rc-kid/rckid-v1/assets/backgrounds/unicorns-black.png

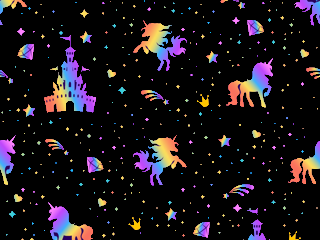
assets/backgrounds/unicorns-black.png
