rc-kid/rckid-v1/assets/heart-white.png

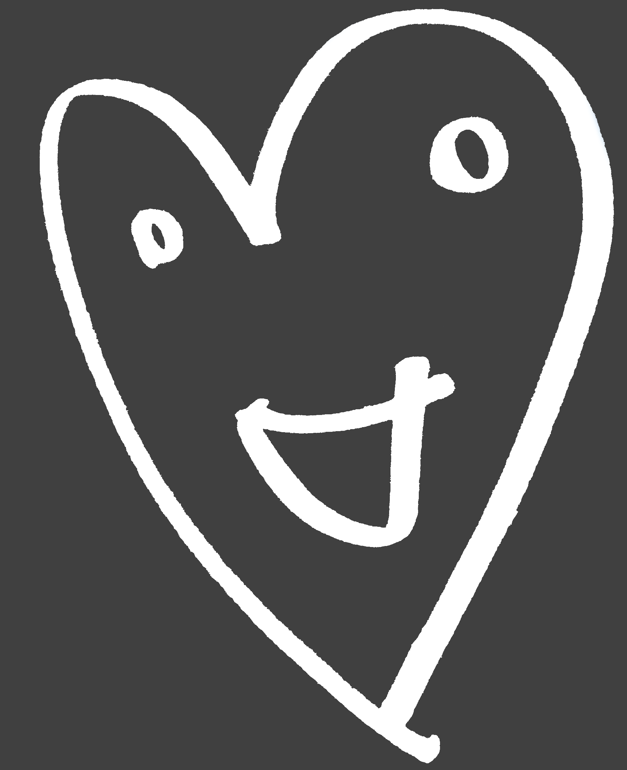
assets/heart-white.png
