rc-kid/rckid-v1/assets/images/001-game-controller.png

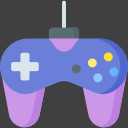
assets/images/001-game-controller.png
