rc-kid/rckid-v1/assets/images/002-rc-car.png

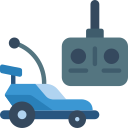
assets/images/002-rc-car.png
