rc-kid/rckid-v1/assets/images/004-flashlight.png

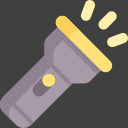
assets/images/004-flashlight.png
