rc-kid/rckid-v1/assets/images/006-baby-crib.png

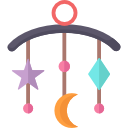
assets/images/006-baby-crib.png
