rc-kid/rckid-v1/assets/images/008-unicorn.png

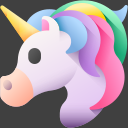
assets/images/008-unicorn.png
