rc-kid/rckid-v1/assets/images/010-high-volume.png

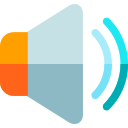
assets/images/010-high-volume.png
