rc-kid/rckid-v1/assets/images/011-power-off.png

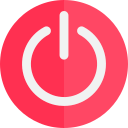
assets/images/011-power-off.png
