rc-kid/rckid-v1/assets/images/012-airplane-mode.png

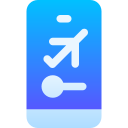
assets/images/012-airplane-mode.png
