rc-kid/rckid-v1/assets/images/014-info.png

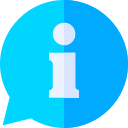
assets/images/014-info.png
