rc-kid/rckid-v1/assets/images/020-poo.png

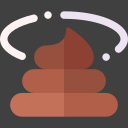
assets/images/020-poo.png
