rc-kid/rckid-v1/assets/images/024-santa-hat.png

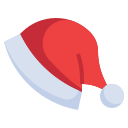
assets/images/024-santa-hat.png
