rc-kid/rckid-v1/assets/images/027-fairy.png

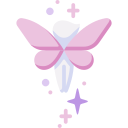
assets/images/027-fairy.png
