rc-kid/rckid-v1/assets/images/031-garbage-car.png

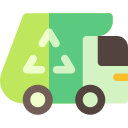
assets/images/031-garbage-car.png
