rc-kid/rckid-v1/assets/images/032-chase.png

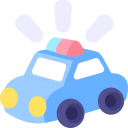
assets/images/032-chase.png
