rc-kid/rckid-v1/assets/images/033-ambulance.png

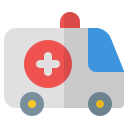
assets/images/033-ambulance.png
