rc-kid/rckid-v1/assets/images/034-fire-truck.png

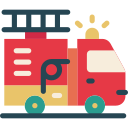
assets/images/034-fire-truck.png
