rc-kid/rckid-v1/assets/images/037-bike.png

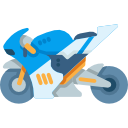
assets/images/037-bike.png
