rc-kid/rckid-v1/assets/images/038-convertible-car.png

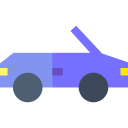
assets/images/038-convertible-car.png
