rc-kid/rckid-v1/assets/images/039-car.png

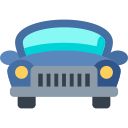
assets/images/039-car.png
