rc-kid/rckid-v1/assets/images/040-baby-carriage.png

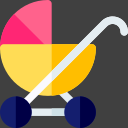
assets/images/040-baby-carriage.png
