rc-kid/rckid-v1/assets/images/041-buggy.png

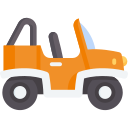
assets/images/041-buggy.png
