rc-kid/rckid-v1/assets/images/043-toy-train.png

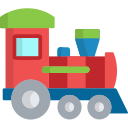
assets/images/043-toy-train.png
