rc-kid/rckid-v1/assets/images/044-pet.png

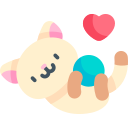
assets/images/044-pet.png
