rc-kid/rckid-v1/assets/images/048-lynx.png

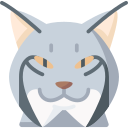
assets/images/048-lynx.png
