rc-kid/rckid-v1/assets/images/051-orca.png

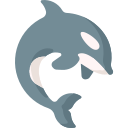
assets/images/051-orca.png
