rc-kid/rckid-v1/assets/images/054-digger.png

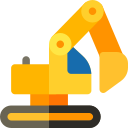
assets/images/054-digger.png
