rc-kid/rckid-v1/assets/images/055-bulldozer.png

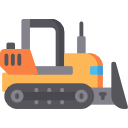
assets/images/055-bulldozer.png
