rc-kid/rckid-v1/assets/images/056-forklift.png

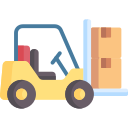
assets/images/056-forklift.png
