rc-kid/rckid-v1/assets/images/057-cinderella-shoe.png

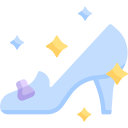
assets/images/057-cinderella-shoe.png
