rc-kid/rckid-v1/assets/images/058-cinderella-carriage.png

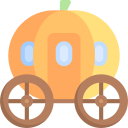
assets/images/058-cinderella-carriage.png
