rc-kid/rckid-v1/assets/images/061-playlist.png

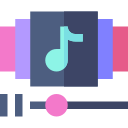
assets/images/061-playlist.png
