rc-kid/rckid-v1/assets/images/066-pause.png

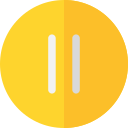
assets/images/066-pause.png
