rc-kid/rckid-v1/assets/images/070-pen-drive.png

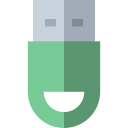
assets/images/070-pen-drive.png
