rc-kid/rckid-v1/assets/images/073-car-engine.png

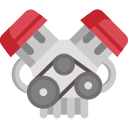
assets/images/073-car-engine.png
