rc-kid/rckid-v1/assets/images/074-siren.png

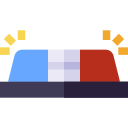
assets/images/074-siren.png
