rc-kid/rckid-v1/assets/images/075-horn.png

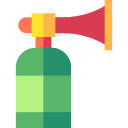
assets/images/075-horn.png
