rc-kid/rckid-v1/assets/images/077-wardrobe.png

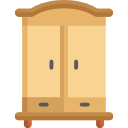
assets/images/077-wardrobe.png
