rc-kid/rckid-v1/assets/images/078-witch.png

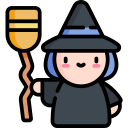
assets/images/078-witch.png
