rc-kid/rckid-v1/assets/images/080-dragon.png

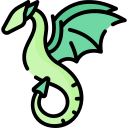
assets/images/080-dragon.png
