rc-kid/rckid-v1/assets/images/082-hourglass.png

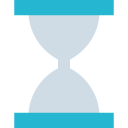
assets/images/082-hourglass.png
