rc-kid/rckid-v1/assets/images/084-spy.png

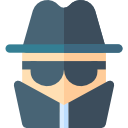
assets/images/084-spy.png
