rc-kid/rckid-v1/assets/images/085-detective.png

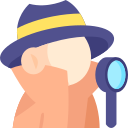
assets/images/085-detective.png
