rc-kid/rckid-v1/assets/images/086-fairy-1.png

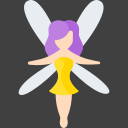
assets/images/086-fairy-1.png
