rc-kid/rckid-v1/assets/images/087-fairy-tale.png

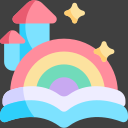
assets/images/087-fairy-tale.png
