rc-kid/rckid-v1/assets/images/088-rose.png

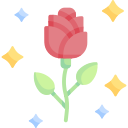
assets/images/088-rose.png
