rc-kid/rckid-v1/assets/images/089-fairy-2.png

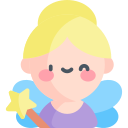
assets/images/089-fairy-2.png
