rc-kid/rckid-v1/assets/images/090-fairy-3.png

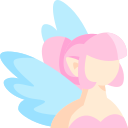
assets/images/090-fairy-3.png
