rc-kid/rckid-v1/assets/images/091-fairy-tale-1.png

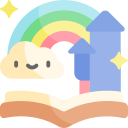
assets/images/091-fairy-tale-1.png
