rc-kid/rckid-v1/assets/images/092-like.png

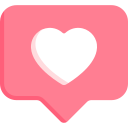
assets/images/092-like.png
