rc-kid/rckid-v1/assets/images/093-duck.png

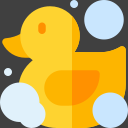
assets/images/093-duck.png
