rc-kid/rckid-v1/assets/images/094-mushroom.png

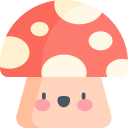
assets/images/094-mushroom.png
