rc-kid/rckid-v1/assets/images/096-dahlia.png

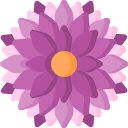
assets/images/096-dahlia.png
