rc-kid/rckid-v1/assets/images/097-heart-1.png

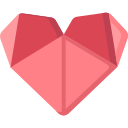
assets/images/097-heart-1.png
