rc-kid/rckid-v1/assets/images/098-train.png

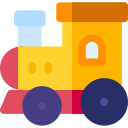
assets/images/098-train.png
