rc-kid/rckid-v1/assets/images/099-mouse.png

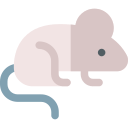
assets/images/099-mouse.png
