rc-kid/rckid-v1/assets/images/100-tulip.png

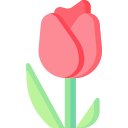
assets/images/100-tulip.png
