rc-kid/rckid-v1/datasheets/ili9341_2-8.png

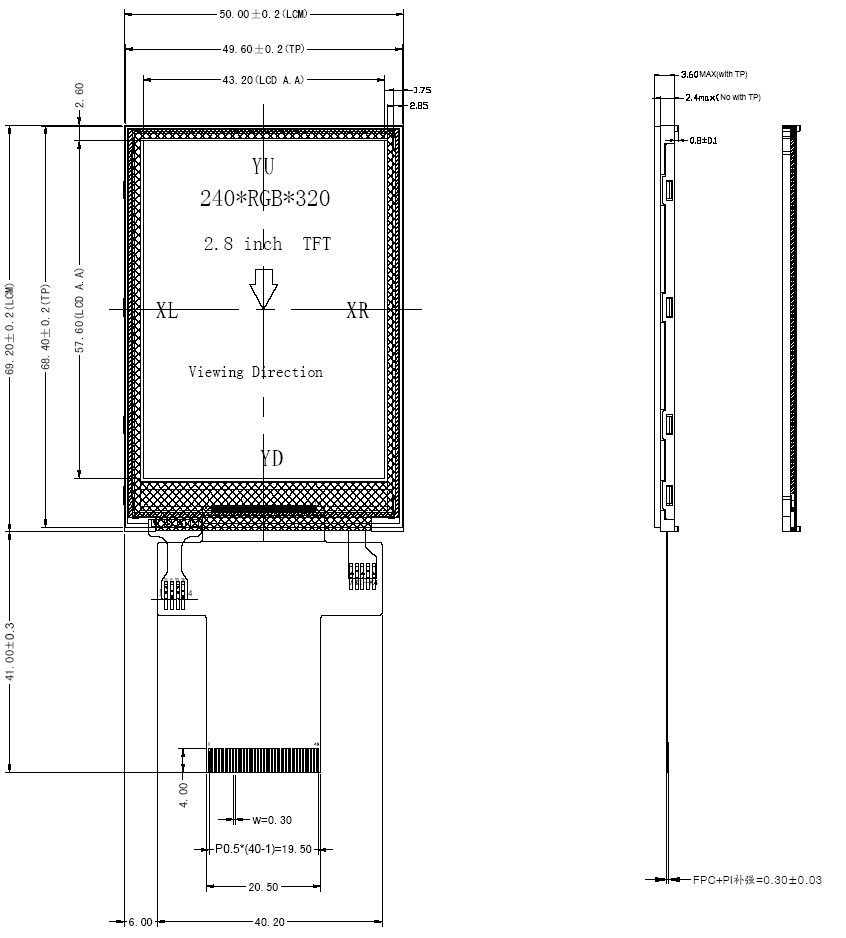
datasheets/ili9341_2-8.png
