rc-kid/rckid-v1/datasheets/ILI9341_3-2-full.jpg

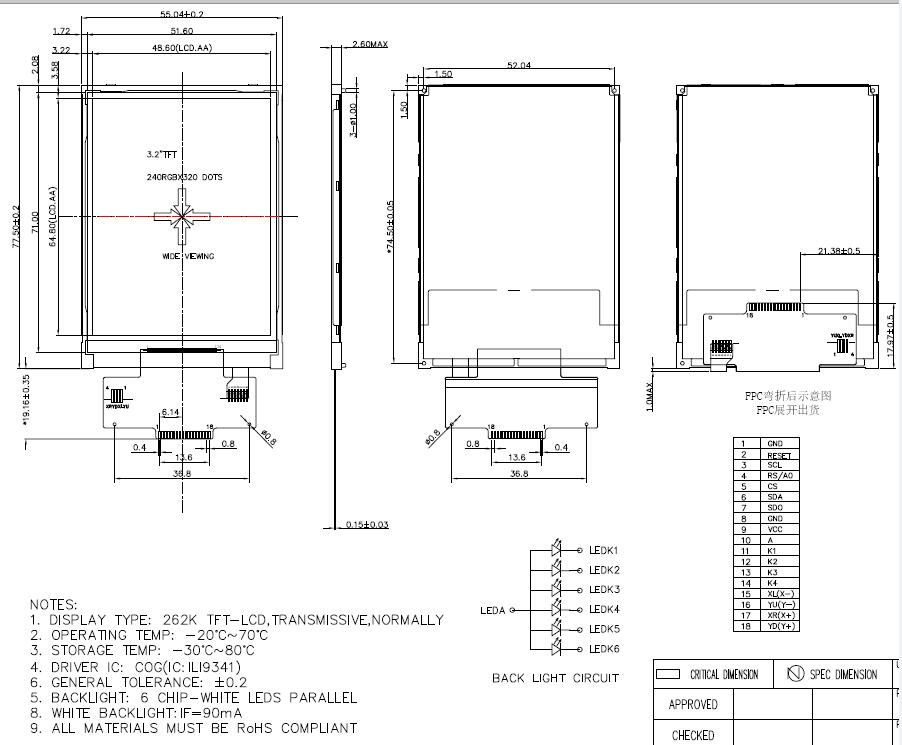
datasheets/ILI9341_3-2-full.jpg
