rc-kid/rckid-v1/datasheets/ili9341_3-2.jpg

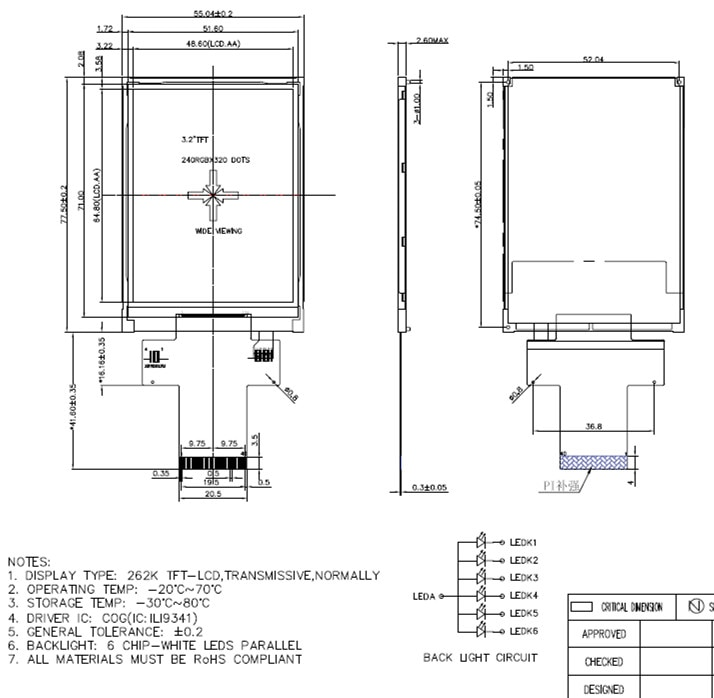
datasheets/ili9341_3-2.jpg
