rc-kid/rckid-v1/datasheets/ili9341_connector_1.jpg

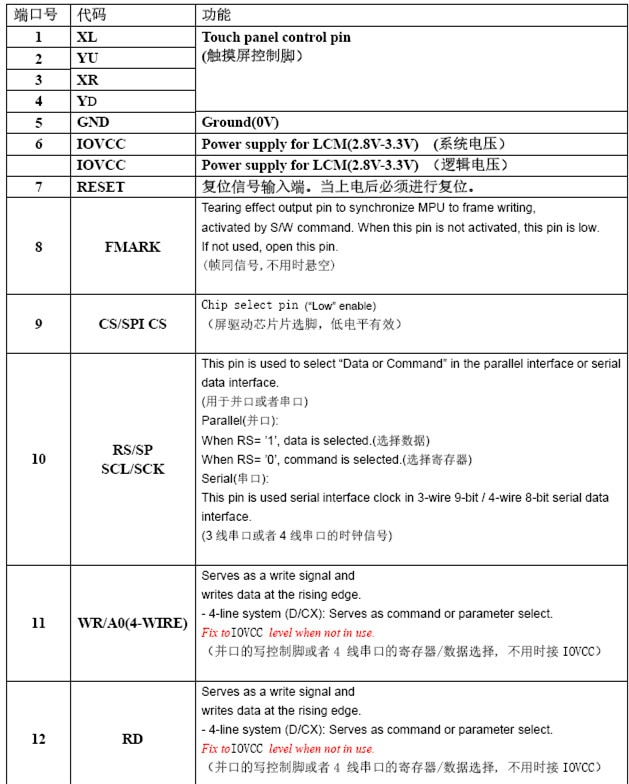
datasheets/ili9341_connector_1.jpg
