rc-kid/rckid-v1/rckid/common/comms.h

#pragma once

#if (defined ARCH_MOCK | defined ARCH_RPI)
    #include <iostream>
#endif

#include "platform/platform.h"
#include "platform/color.h"
#include "platform/time.h"

#include "config.h"
#include "../avr-i2c-bootloader/src/bootloader_config.h"

namespace comms {

    /** Power-related Modes the RCKid can be in. 

        When the BTN_HOME button is pressed, we enter the `PoweringUp` mode, in which the power to RPI is enabled and the RPI starts to boot. The AVR also times the length of the BTN_HOME press. If the press duration goes over the POWER_ON_PRESS_THRESHOLD_TICKS, the rumbler is signalled. If the btn button is pressed for a shorter period, mode changes to `PoweringDown`.

        Eventually the RPi will contact the AVR, changing the mode from `PoweringOn` to `On`.  If the mode is already `PoweringDown`, the RPi should power itself off immediately, otherwise it starts working normally and AVR enabled the backlight.   

        When in the `PoweringDown` mode, the AVR waits for the `RPI_POWEROFF` signal to go up, at which point it turns the power to Rpi off and changes mode to sleep.  

        After power on, the default mode is `On`.  
     */
    enum class Mode : uint8_t { // 8 modes are available
        On = 0,  // also dubs as initial recording batch index (we only record in On mode)
        Sleep = 1, 
        WakeUp = 2,
        PowerUp = 3,
        PowerDown = 4,
        Bootloader = bootloader::BOOTLOADER_MODE,
    }; // comms::Mode

    /** Current power mode of the device. 
     */
    enum class PowerStatus : uint8_t {
        Battery = 0, 
        LowBattery = 64, 
        Charging = 128, 
        USB = 192,
    }; // comms::PowerStatus

    /** Error codes. 
     
        The extended state also contains an information about the error state the RCKid is in. While not all states are really errors (such as initial power on), they should all be inspected, reported and logged by the RPi appropriately. Depending on the error state. For some states, the RGB LED also illustrates what is going on. 
    */
    enum class ErrorCode : uint8_t {
        /// no error condition present
        NoError, 
        /// initial power on (not an error condition)
        InitialPowerOn,
        /// AVR watchdog timed out
        WatchdogTimeout,
        /// RPi failed to boot in time 
        RPiBootTimeout,
        /// RPi failed to power down in the specified timeout
        RPiPowerDownTimeout,
    }; 

    /** The AVR status. 

        Every I2C communication with the AVR always returns the status as the first byte. 
     */
    class Status {
    public:

        Mode mode() const { return recording() ? Mode::On : static_cast<Mode>(status_ & MODE); }

        void setMode(Mode mode) {
            status_ = status_ & ~MODE;
            status_ |= static_cast<uint8_t>(mode);
        }

        bool recording() const { return status_ & RECORDING; }

        bool setRecording(bool value) { 
            if (value == recording())
                return false;
            value ? (status_ |= RECORDING) : (status_ &= ~RECORDING);
            return true;
        }

        bool alarm() const { return status_ & ALARM; }

        bool setAlarm(bool value) { 
            if (value == alarm())
                return false;
            value ? (status_ |= ALARM) : (status_ &= ~ALARM);
            return true;
        }

        /** In recording mode, returns the index of the next batch that will be returned if the reading continues.
         */
        uint8_t batchIndex() const {
            return status_ & MODE;
        }

        void setBatchIndex(uint8_t index) {
            status_ &= ~MODE;
            status_ |= (index & MODE);
        }

        bool batchIncomplete() const {
            return status_ & BATCH_INCOMPLETE;
        }

        bool setBatchIncomplete(bool value) {
            if (value == batchIncomplete())
                return false;
            value ? (status_ |= BATCH_INCOMPLETE) : (status_ &= ~BATCH_INCOMPLETE);
            return true;
        }

        PowerStatus powerStatus() const { 
            return static_cast<PowerStatus>(status_ & POWER_MASK); 
        }

        bool setPowerStatus(PowerStatus value) {
            if (value == powerStatus())
                return false;
            status_ &= ~POWER_MASK;
            status_ |= static_cast<uint8_t>(value);
            return true;
        }

    private:

        static constexpr uint8_t MODE = 7; // 0..7
        static constexpr uint8_t ALARM = 1 << 3; // 8
        static constexpr uint8_t RECORDING = 1 << 4; // 16
        static constexpr uint8_t BATCH_INCOMPLETE = 1 << 5; // 32
        static constexpr uint8_t POWER_MASK = 3 << 6; // 64 + 128
        uint8_t status_ = 0;


#if (defined ARCH_RPI || defined ARCH_MOCK)
        friend std::ostream & operator << (std::ostream & s, Status const & status) {
            if (status.recording())
                s << "mode : recording, batch index: " << (int)status.batchIndex();
            else
                s << "mode " << (int) status.mode();
            s  << ", batch incomplete:" << status.batchIncomplete() << ", alarm: " << status.alarm() << ", low batt: ";
            return s;
        }
#endif

    } __attribute__((packed)); // comms::Status

    /** Information about the input controls connected to the RPi. 
    */
    class Controls {
    public:

        bool home() const { return buttons_ & HOME; }
        bool select() const { return buttons_ & SELECT; }
        bool start() const { return buttons_ & START; }
        bool triggerLeft() const { return buttons_ & TRIGGER_LEFT; }
        bool triggerRight() const { return buttons_ & TRIGGER_RIGHT; }

        /** \name Sets the button values. 
         
            Note that these "hacky" functions require the button's bits to align with the bits reported by the analog button decoder. 
        */
        //@{
        bool setButtons1(uint8_t btns1) { return setButtonsRaw(btns1 & 0x03, 0x03); }

        bool setButtons2(uint8_t btns2) { return setButtonsRaw((btns2 & 0x03) << 2, 0x03 << 2); }

        bool setButtonHome(bool value) { 
            if (value == home())
                return false;
            value ? buttons_ |= HOME : buttons_ &= ~HOME;
            return true;
        }  

        void setSelect(bool value = true) { value ? buttons_ |= SELECT : buttons_ &= ~SELECT; }  
        void setStart(bool value = true) { value ? buttons_ |= START : buttons_ &= ~START; }  
        void setTriggerLeft(bool value = true) { value ? buttons_ |= TRIGGER_LEFT : buttons_ &= ~TRIGGER_LEFT; }  
        void setTriggerRight(bool value = true) { value ? buttons_ |= TRIGGER_RIGHT : buttons_ &= ~TRIGGER_RIGHT; }  
        //@}

        uint8_t joyH() const { return joyH_; }

        bool setJoyH(uint8_t value) {
            if (value == joyH_)
                return false;
            joyH_ = value;
            return true;
        }

        uint8_t joyV() const { return joyV_; }

        bool setJoyV(uint8_t value) {
            if (value == joyV_)
                return false;
            joyV_ = value;
            return true;
        }

 
    private:

        bool setButtonsRaw(uint8_t value, uint8_t mask) {
            uint8_t btns = (buttons_ & ~mask) | value;
            if (btns == buttons_)
                return false;
            buttons_ = btns;
            return true;
        }

        static constexpr uint8_t SELECT = 1 << 0;
        static constexpr uint8_t TRIGGER_LEFT = 1 << 1;
        static constexpr uint8_t START = 1 << 2;
        static constexpr uint8_t TRIGGER_RIGHT = 1 << 3;
        static constexpr uint8_t HOME = 1 << 4;

        uint8_t buttons_;
        uint8_t joyH_;
        uint8_t joyV_;
    } __attribute__((packed)); // comms::Controls 

    class ExtendedInfo {
    public:

        /** \name VCC
         
            The voltage to the AVR measured in 0.01[V]. Value of 0 means any voltage below 2.46V, value of 500 5V or more, otherwise the number returnes is volatge * 100. 
         */
        //@{
        uint16_t vcc() const { return (vcc_ == 0) ? 0 : (vcc_ + 245); }

        void setVcc(uint16_t vx100) {
            if (vx100 < 250)
                vcc_ = 0;
            else if (vx100 >= 500)
                vcc_ = 255;
            else 
                vcc_ = (vx100 - 245) & 0xff;
        }
        //@}

        /** \name VBATT
         
            Battery voltage. Measured in 0.01[V] in rangle from 1.7V to 4.2V. 420 means 4.2V or more, 0 means 1.7V or less.
         */
        //@{
        uint16_t vBatt() const { return (vbatt_ == 0) ? 0 : vbatt_ + 165; }

        void setVBatt(uint16_t vx100) {
            if (vx100 >= 420)
                vbatt_ = 255;
            else if (vx100 < 170)
                vbatt_ = 0;
            else 
                vbatt_ = (vx100 - 165) & 0xff;
        }
        //@}

        /** \name Temperature 
         
            Returns the temperature as measured by the chip with 0.1[C] intervals. -200 is -20C or less, 1080 is 108[C] or more. 0 is 0C. 
         */
        //@{
        int16_t temp() const { return -200 + (temp_ * 5); }

        void setTemp(int32_t tempx10) {
            if (tempx10 <= -200)
                temp_ = 0;
            else if (tempx10 >= 1080)
                temp_ = 255;
            else 
                temp_ = (tempx10 + 200) / 5;
        }
        //@}

    private:
        uint8_t vcc_;
        uint8_t vbatt_;
        uint8_t temp_;
    } __attribute__((packed)); // comms::ExtendedInfo;

    /** State consists  */
    class State {
    public:
       Status status;
       Controls controls;
    } __attribute__((packed)); // comms::State

    static_assert(sizeof(State) == 4);


    class DebugInfo {
    public:
        ErrorCode errorCode() const { return static_cast<ErrorCode>(raw_ & ERROR_CODE); }

        void setErrorCode(ErrorCode code) {
            raw_ &= ~ERROR_CODE;
            raw_ |= static_cast<uint8_t>(code) & ERROR_CODE;
        }

        bool clear() {
            if (errorCode() != ErrorCode::NoError) {
                setErrorCode(ErrorCode::NoError);
                return true;
            } else {
                return false;
            }
        }
    
    private:
        static constexpr uint8_t ERROR_CODE = 15;
        // 4 free bits
        uint8_t raw_;

    } __attribute__((packed)); // comms::DebugInfo

    class ExtendedState {
    public:
        Status status;
        Controls controls;
        ExtendedInfo einfo;
        DebugInfo dinfo;
        utils::DateTime time;
        uint32_t uptime = 0;
    } __attribute__((packed));// comms::ExtendedState

    static_assert(sizeof(ExtendedState) <= 32);

    /** Persistent data that we back up in the AVR between RPi runs, but which the RPi itself is in charge of wrt changes. 
     */
    struct PersistentState {
        utils::DateTime alarm;
        uint8_t brightness{128};
        uint8_t volume{50};
        // number of heart seconds available for protected contents
        uint16_t hearts{3600};
        // joystick calibration - min and max raw values for the horizontal and vertical axes
        uint8_t joyHMin{49};
        uint8_t joyHMax{215};
        uint8_t joyVMin{59};
        uint8_t joyVMax{225};
    } __attribute__((packed)); // comms::PersistentState

    static_assert(sizeof(PersistentState) <= 31); // needs to be 31 so that we can have it as arg to message when saving to AVR (1 byte taken up by the msg id)

} // namespace comms

/** \name Messages
 
    The AVR and RPi communicate with each other via typed messages whose kinds and payloads are defined below. All messages have automatically assigned id numbers. As a side-effect the avr and rpi versions must be identical or the message ids may differ, which would lead to problems. 
 */

#define MESSAGE(NAME, ...) \
    class NAME : public msg::MessageHelper<NAME> { \
    public: \
        static uint8_t constexpr ID = __COUNTER__ - COUNTER_OFFSET; \
        static NAME const & fromBuffer(uint8_t const * buffer) { \
            return * reinterpret_cast<NAME const *>(buffer); \
        } \
        __VA_ARGS__ \
    } __attribute__((packed))

namespace msg {

    class Message {
    public:
        uint8_t const id;

        /*
        template<typename T> T const & fromBuffer(uint8_t const * buffer) {
            return * reinterpret_cast<T const *>(buffer);
        } */

    protected:
        Message(uint8_t id): id{id} {}
        static int constexpr COUNTER_OFFSET = __COUNTER__ + 1;
    };

    template<typename T> class MessageHelper : public Message {
    public:
        MessageHelper():Message{T::ID} {}
    }; // MessageHelper<T>

    /** First message is NOP. This is for compatibility with the bootloader where message 0x00 is reserved. 
     */
    MESSAGE(Nop);
    static_assert(Nop::ID == 0);

    /** Causes the reset of the AVR chip. 
     
        Useful for debugging and programming via the I2C interface. Reset in the AVR mode is the same as in the bootloader. 
     */
    MESSAGE(AvrReset);
    static_assert(AvrReset::ID == 1);

    /** Returns the chip information. This is identical to the bootloader and can be used to get chip information after it has been programmed. 
     */
    MESSAGE(Info);
    static_assert(Info::ID == 2);

    /** Starts the audio recording. 
    */
    MESSAGE(StartAudioRecording);
    /** Stops the audio recording.
     */
    MESSAGE(StopAudioRecording);

    /** Sets the brightness of the TFT screen. 
     */
    MESSAGE(SetBrightness,
        uint8_t value;
        SetBrightness(uint8_t value): value{value} {}
    );

    MESSAGE(SetTime, 
        utils::DateTime value;
        SetTime(utils::DateTime value): value{value} {}
    );

    MESSAGE(GetPersistentState);

    MESSAGE(SetPersistentState,
        comms::PersistentState pState; 
        SetPersistentState(comms::PersistentState const & pState): pState{pState} {}
    );

    MESSAGE(RumblerOk);
    MESSAGE(RumblerFail);

    MESSAGE(Rumbler,
        uint8_t intensity;
        uint16_t duration; // duration in 10ms intervals
        Rumbler(uint8_t intensity, uint16_t duration): intensity{intensity}, duration{duration} {}
    );


    MESSAGE(RGBOn);
    MESSAGE(RGBOff);

    MESSAGE(RGBColor, 
        platform::Color color;
        RGBColor(platform::Color color): color{color} {}
    );

    /** Informs the AVR that the raspberry pi has been powered on and is working. 
     
        Clears the power up mode timeout and moves to the On mode with periodic AVR status check intervals. 
     */
    MESSAGE(PowerOn);

    /** Powers the raspberry pi off and moves the avr into a standby state. 
     
        The poweroff is not immediate since RPI must 
     */
    MESSAGE(PowerDown);

    /** Clears the debug info extended status part, also turns the RGB off in case it was displaying the error.
     */
    MESSAGE(DInfoClear);

} // namespace msg

#undef MESSAGE
