rc-kid/rckid-v1/rckid/rpi/nrf_sniffer.h

#pragma once

#include <deque>

#include "widget.h"
#include "window.h"

/** A simple NRF sniffer class that displays received messages, which is useful for testing
    
 */
class NRFSniffer : public Widget {
public:

protected:

    void draw(Canvas & c) override {
        BeginBlendMode(BLEND_ADD_COLORS);
        c.drawText(0, 200, STR("TX: " << tx_ << " RX: " << rx_ << " /s: " << packetsPerLastSecond_), WHITE);
        c.setFont(c.helpFont());
        for (size_t i = 0; i < msgs_.size(); ++i) {
            size_t id = (rx_ - msgs_.size() + i) % 1000;
            c.drawText(0, 20 + 18 * i, STR(id << ":"), DARKGRAY);
            //window().helpFont(), STR(id << ":").c_str(), 0, 20 + 18 * i, 16, 1.0, DARKGRAY);
            c.drawText(32, 20 + 18 * i, msgs_[i].bytesToStr(0, 8), WHITE);
            c.drawText(145, 20 + 18 * i, ":", DARKGRAY);
            c.drawText(153, 20 + 18 * i, msgs_[i].bytesToStr(8, 8), WHITE);
        }
    }

    void setFooterHints() override {
        Widget::setFooterHints();
        window().addFooterItem(FooterItem::A("Start/Stop"));
        window().addFooterItem(FooterItem::X("Reset"));
    }

    void onNavigationPush() override {
        lastSecond_ = now();
        packetsPerSecond_ = 0;

        rckid().nrfInitialize(rxAddr_.c_str(), txAddr_.c_str(), channel_);
        rckid().nrfEnableReceiver();
        /*
        if (msgs_.empty()) {
            msgs_.push_back(Message{"0123456789", 10});
            ++tx_;
        } */
    }

    void onNavigationPop() override {
        rckid().nrfPowerDown();
    }

    void btnA(bool state) override {
        if (state) {
            if (running_) {
                running_ = false;
                rckid().nrfPowerDown();
            } else {
                running_ = true;
                rckid().nrfInitialize(rxAddr_.c_str(), txAddr_.c_str(), channel_);
                rckid().nrfEnableReceiver();
            }
        }
    }

    void btnX(bool state) override {
        if (state) {
            msgs_.clear();
            rx_ = 0;
            tx_ = 0;
        }
    }

    void nrfPacketReceived(NRFPacketEvent & e) override {
        ++rx_;
        msgs_.push_back(Message{e.packet});
        while (msgs_.size() > 8) {
            ++ packetsPerSecond_;
            msgs_.pop_front();
        }
        Timepoint t = now();

        if (asMillis(t - lastSecond_) >= 1000 ) {
            lastSecond_ = t;
            packetsPerLastSecond_ = packetsPerSecond_;
            packetsPerSecond_ = 0;
        }
    }

private:

    struct Message {
        uint8_t packet[32];

        Message(uint8_t const * packet, size_t length = 32) {
            memcpy(this->packet, packet, length);
        }

        Message(char const * packet, size_t length = 32) {
            memcpy(this->packet, packet, length);
        }

        std::string bytesToStr(size_t start, size_t num) {
            std::stringstream ss;
            while (num-- > 0) {
                ss << "0123456789abcdef"[packet[start] / 16];
                ss << "0123456789abcdef"[packet[start++] % 16];
            }
            return ss.str();
        }

    };

    bool running_ = true;
    std::string rxAddr_ = "AAAAA";
    std::string txAddr_ = "AAAAA";
    uint8_t channel_ = 86;
    size_t rx_ = 0;
    size_t tx_ = 0;
    size_t packetsPerSecond_ = 0;
    size_t packetsPerLastSecond_ = 0;
    Timepoint lastSecond_;

    std::deque<Message> msgs_;


}; 
