rc-kid/rckid-v1/rckid/rpi/widget.cpp

#include "window.h"
#include "widget.h"

bool Widget::focused() const { 
    Window * w = & window();
    return (w != nullptr && w->activeWidget() == this);
}

void Widget::btnB(bool state) {
    if (state)
        window().back();
}

void Widget::btnHome(bool state) {
    if (state)
        window().showHomeMenu(); 
}

void Widget::setFooterHints() {
    window().resetFooter();
}
